kershen-bot/Custom-Computers/3D Moduls/Speaker.stl

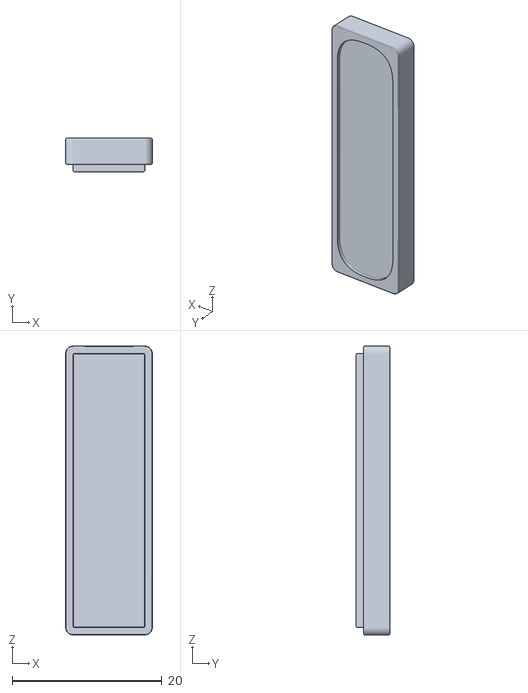
[picture p16: CAD file, 2026-06-09]
3D Moduls/Speaker.stl
11.6 x 4.50 x 38.6
