kershen-bot/Custom-Computers/3D Moduls/Hinge Pin - Hinge Pin.stl

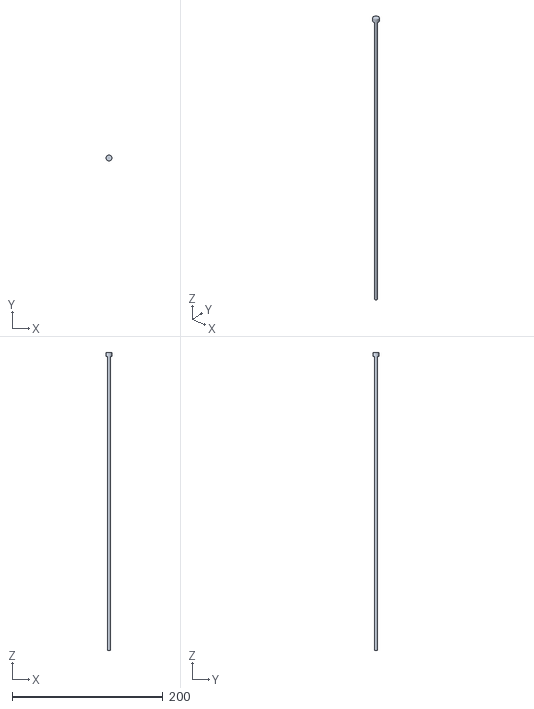
[picture p17: CAD file, 2026-06-09]
3D Moduls/Hinge Pin - Hinge Pin.stl
8.00 x 8.00 x 395.0
