kershen-bot/Custom-Computers/3D Moduls/LattePanda_Mu.step

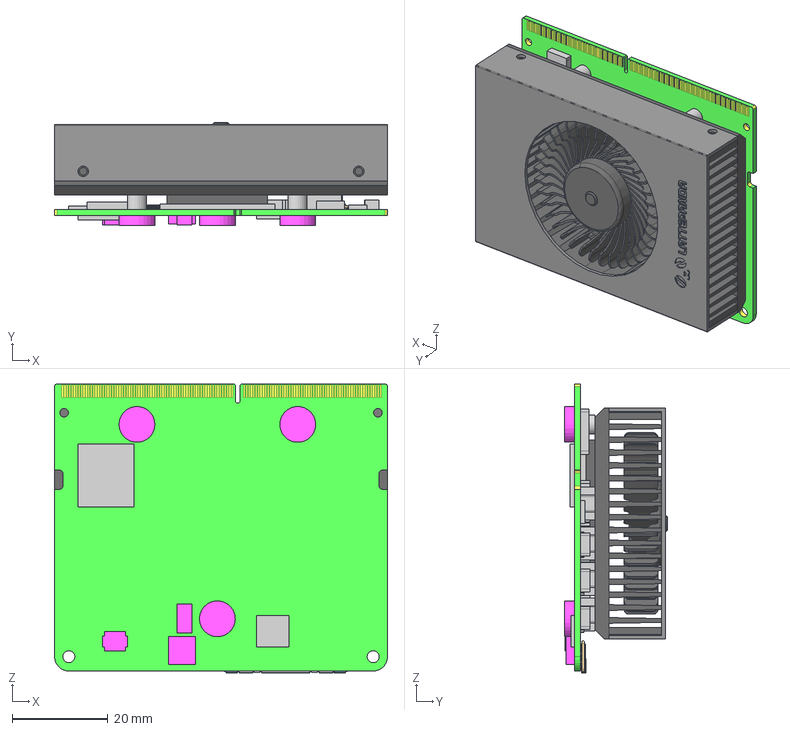
[picture p18: CAD file, 2026-06-09]
3D Moduls/LattePanda_Mu.step
69.6 x 21.5 x 60.4 mm
LV0505-R40X
LV0505H-H40X
LV0504-40-0010RA-G3
BREP_1
BREP_2
_X2_5B9E4F53_X0_1
BREP_9
BREP_10
BREP_11
BREP_13
FPC0510-06B2-G1R
FPC0510-24B2-G1R
S70NC1R100
CPU
SML_7P0X6P6_3P0H x 4
CAP_2_7D3X4D3_H1D9 x 4
CAP_2_3D5X2D8_H1D9 x 3
QFN19_0D5_3X4_H0D9
TK1_LCC21_3100X5100_400_MA x 3
