kershen-bot/Custom-Computers/3D Moduls/Trackpad.stl

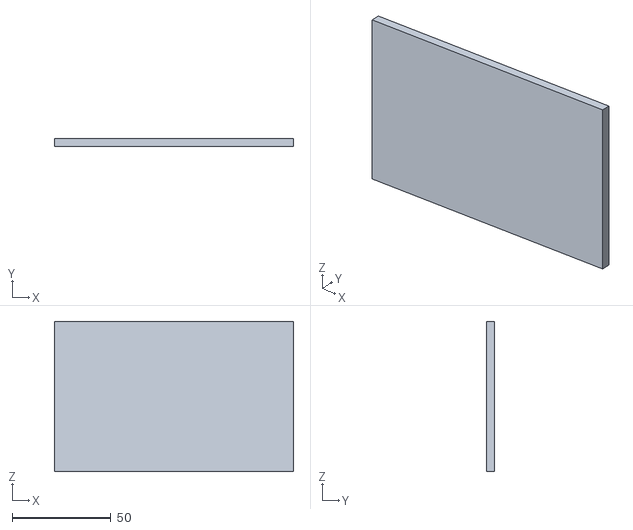
[picture p19: CAD file, 2026-06-09]
3D Moduls/Trackpad.stl
121.0 x 4.08 x 76.0
