kershen-bot/Custom-Computers/3D Moduls/Hinge Pin End - Hinge Pin End.stl

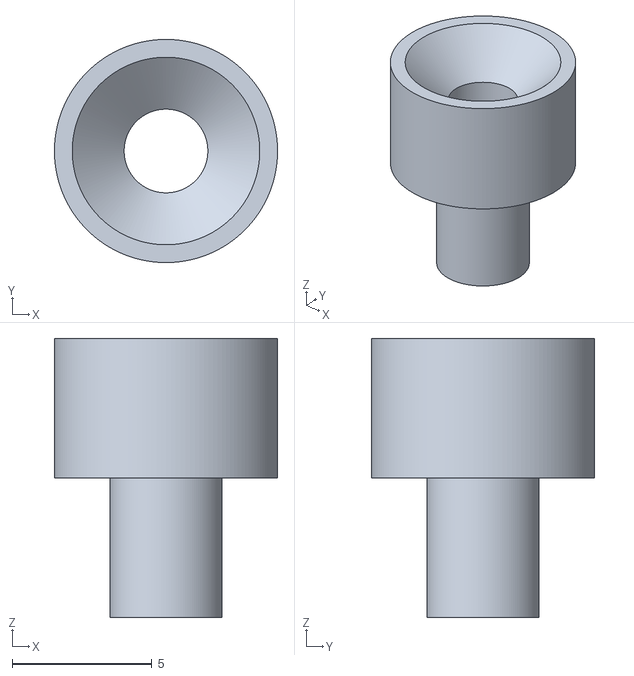
[picture p20: CAD file, 2026-06-09]
3D Moduls/Hinge Pin End - Hinge Pin End.stl
8.00 x 8.00 x 10.0
