kershen-bot/Custom-Computers/3D Moduls/Adafruit TLV320DAC3100 I2S DAC.stl

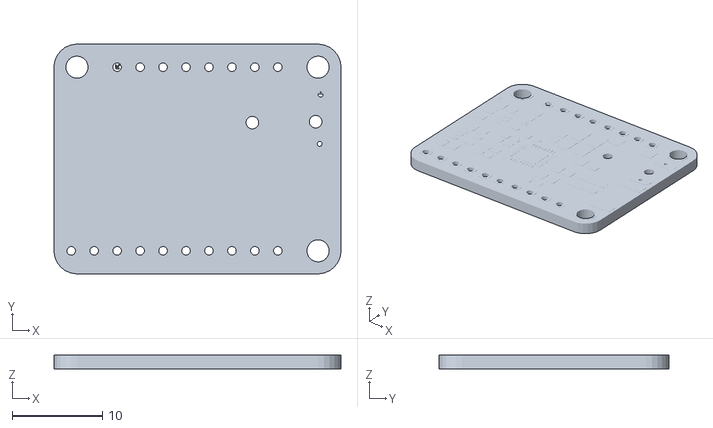
[picture p21: CAD file, 2026-06-09]
3D Moduls/Adafruit TLV320DAC3100 I2S DAC.stl
31.8 x 25.4 x 1.66
