kershen-bot/Custom-Computers/3D Moduls/Top Cover - Top Cover.stl

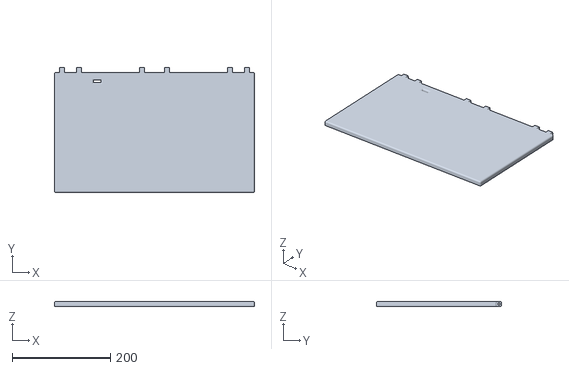
[picture p22: CAD file, 2026-06-09]
3D Moduls/Top Cover - Top Cover.stl
406.4 x 254.0 x 10.0
